ifilot/slot-otter/src/SD.C

/* =====================================================================
 *  Project: SLOT-OTTER
 *  File:    SD.C
 *  Author:  Ivo Filot <ivo@ivofilot.nl>
 *
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
 *  You should have received a copy of the GNU General Public License
 *  along with this program.  If not, see <https://www.gnu.org/licenses/>.
 * ===================================================================== */

#include "sd.h"

/*
 * sd_boot - Boot SD card
 *
 * Returns:
 *      0 if success, otherwise on fail
 */
int sd_boot() {
    int i, j, ctr;
    unsigned char v, c1, c2;
    unsigned char *ptr;
    unsigned char rsp5[5];

    sd_set_miso_high(cfg_get_base_port());

    ctr = 0;
    v = 0xFF;
    while(v != 0x01 & ctr < MAXTRIAL) {
        sddis(cfg_get_base_port());
        cmdclr(cfg_get_base_port());
        sden(cfg_get_base_port());
        v = cmd00(cfg_get_base_port());	/* put card in idle state */
        ctr++;
    }

    if(ctr >= MAXTRIAL) {
        printf("Cannot put card in idle mode.\n");
        printf("Try to reinsert the card.\n");
        sddis(cfg_get_base_port());
        return -1;
    }
    
    printf("CMD00 response: %02X\n", v);
    v = cmd08(cfg_get_base_port(), rsp5);	/* send cmd08 */
    printf("CMD08 response: ");
    
    for(i=0; i<5; ++i) {
        printf("%02X ", rsp5[i]);
    }
    printf("\n");

    /* TRY ACMD41 */
    v = 0xFF;
    ctr = 0;
    while(v != 0x00 && ctr < MAXTRIAL) {
        delay(1); /* wait one ms */
        v = cmd55(cfg_get_base_port());
        if(v == 0xFF) {
            continue;	/* try again on 0xFF */
        }
        v = acmd41(cfg_get_base_port());
        ctr++;
    }

    if(ctr >= MAXTRIAL) {
        printf("Unable to send ACMD41 after %i attempts.\n", ctr);
        return -1;
    } else {
        printf("ACMD41 response: %02X (%i)\n", v, ctr);
    }

    /* CMD58 - READ OCR */
    v = cmd58(cfg_get_base_port(), rsp5);
    printf("CMD58 response: ");
    for(i=0; i<5; ++i) {
        printf("%02X ", rsp5[i]);
    }
    
    printf("\n");
    return 0;
}

/*
 * Pulls the MISO line low
 *
 * Parameters:
 *      ioport - Which base IO address
 */
void sd_set_miso_low(unsigned ioport) {
    outportb(ioport | 0x02, 0xFF);
}

/*
 * Pulls the MISO line high
 *
 * Parameters:
 *      ioport - Which base IO address
 */
void sd_set_miso_high(unsigned ioport) {
    outportb(ioport | 0x03, 0xFF);
}

/*
 * Disables SD card (pulls /ENABLE HIGH)
 *
 * Parameters:
 *      ioport - Which base IO address
 */
void sd_disable(unsigned ioport) {
    sddis(ioport);
}
