ifilot/slot-otter/testing/sdtest/HELPERS.H

#ifndef __HELPERS_H
#define __HELPERS_H

#include <stdio.h>
#include <conio.h>
#include <stdlib.h>

#define BLACKONWHITE 112
#define WHITEONBLACK   7

/*
 * Print 512-block to the screen
 */
void print_block(unsigned char buf[]);

#endif
